Norman-w/smd-component-storage-book/output/3d-print/0603_tape_page_12mm_label12_x1c_petg_v1.3mf

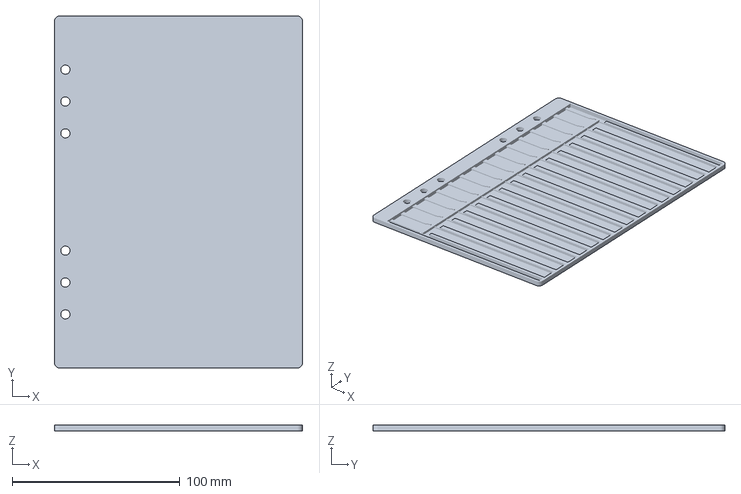
[picture p15: CAD file, 2026-09-22]
output/3d-print/0603_tape_page_12mm_label12_x1c_petg_v1.3mf
148.0 x 210.0 x 3.45 mm
