Norman-w/smd-component-storage-book/output/3d-print/0603_fit_coupon_single_7_16mm_label12_v1.stl

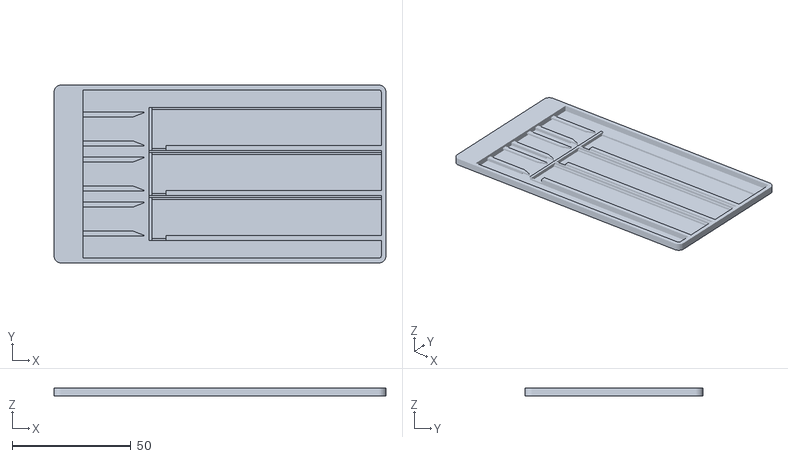
[picture p16: CAD file, 2026-09-22]
output/3d-print/0603_fit_coupon_single_7_16mm_label12_v1.stl
140.0 x 75.0 x 3.45
