Norman-w/smd-component-storage-book/output/3d-print/0603_tape_page_v9_convex_label_mouth.stl

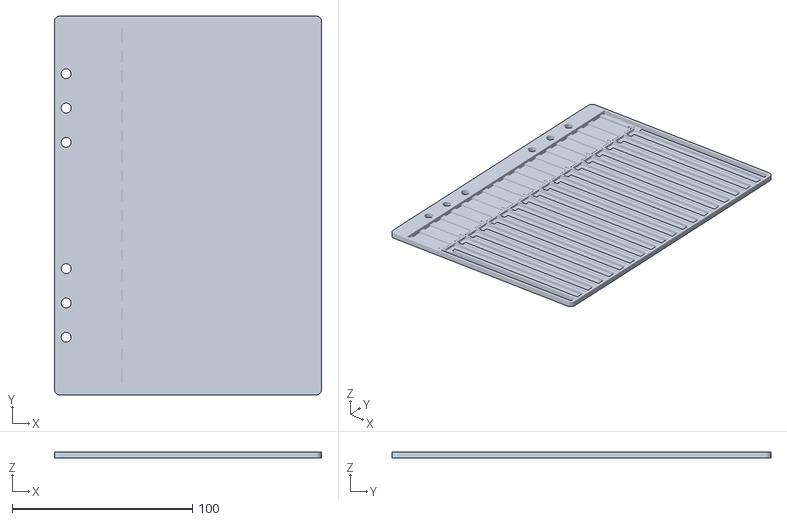
[picture p17: CAD file, 2026-09-20]
output/3d-print/0603_tape_page_v9_convex_label_mouth.stl
148.0 x 210.0 x 3.45
