Norman-w/smd-component-storage-book/output/3d-print/0603_tape_page_v5_thin_partition_x1c_safe.stl

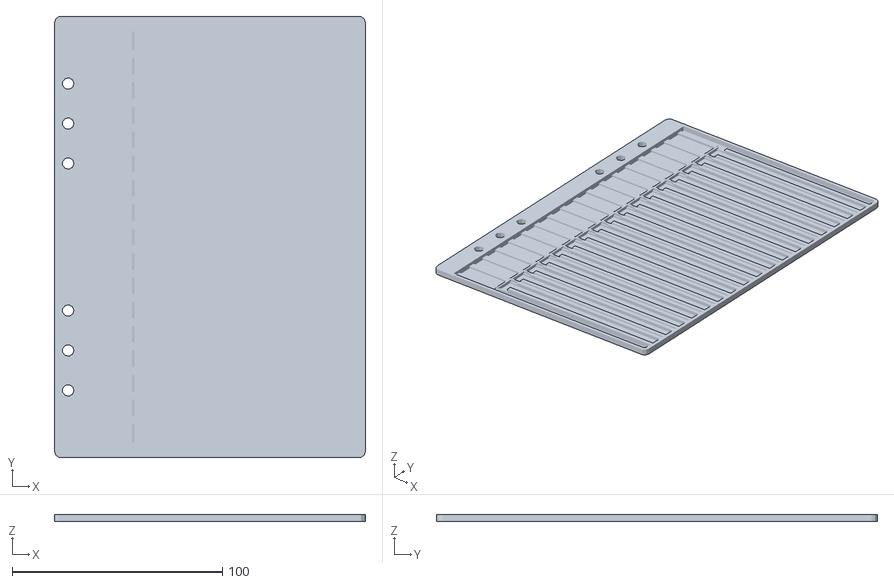
[picture p18: CAD file, 2026-09-20]
output/3d-print/0603_tape_page_v5_thin_partition_x1c_safe.stl
148.0 x 210.0 x 3.45
