Norman-w/smd-component-storage-book/output/3d-print/0603_tape_page_v3.stl

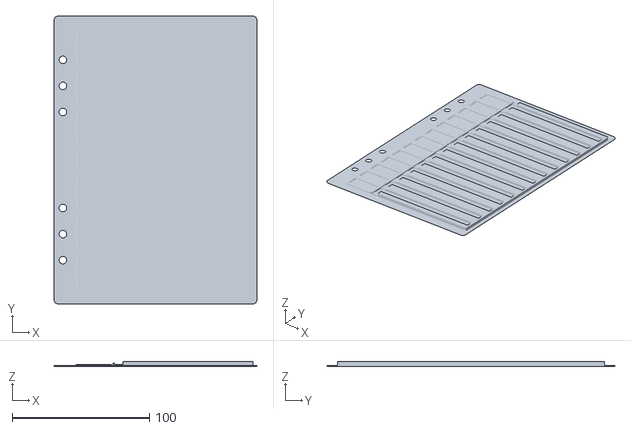
[picture p21: CAD file, 2026-09-20]
output/3d-print/0603_tape_page_v3.stl
148.0 x 210.0 x 3.45
