Norman-w/smd-component-storage-book/output/3d-print/0603_fit_coupon_single_7_v3.stl

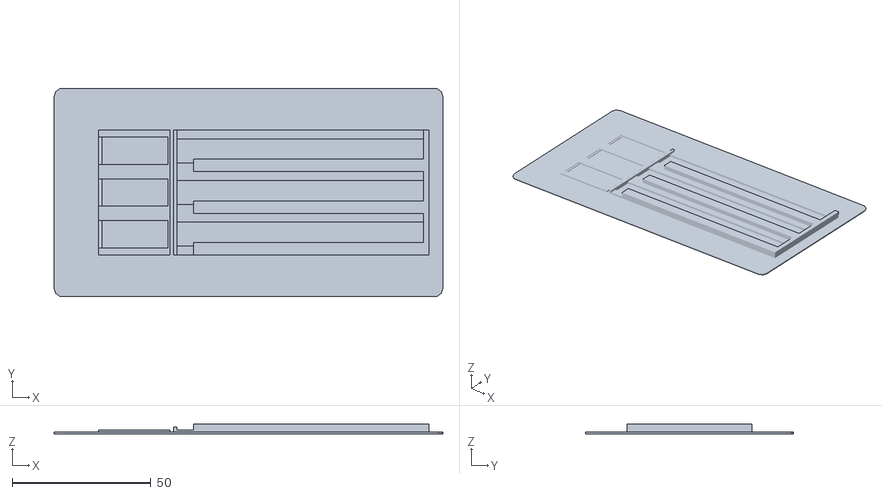
[picture p22: CAD file, 2026-09-20]
output/3d-print/0603_fit_coupon_single_7_v3.stl
140.0 x 74.7 x 3.45
