Norman-w/smd-component-storage-book/output/3d-print/0603_tape_page_v1_x1c_landscape.stl

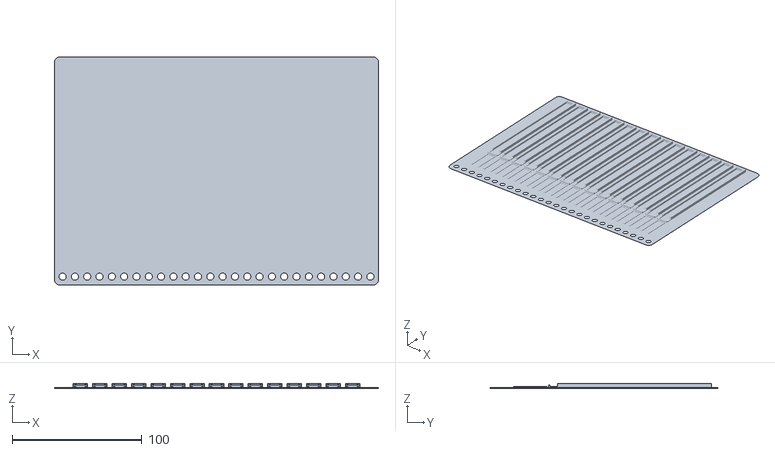
[picture p23: CAD file, 2026-09-20]
output/3d-print/0603_tape_page_v1_x1c_landscape.stl
250.0 x 176.0 x 3.55
