Norman-w/smd-component-storage-book/src/0603_tape_page_16mm_label12_tight_x1c_safe.scad

// X1C-safe wrapper for the compact 16 mm tape / 12 mm label page.
// The page geometry is shifted away from the X1C lower-left calibration area.

translate([54, 23, 0])
    import("../output/3d-print/0603_tape_page_16mm_label12_tight_v1.stl");
