Norman-w/smd-component-storage-book/output/verification/0603_16mm_label12_full_page_isometric.png

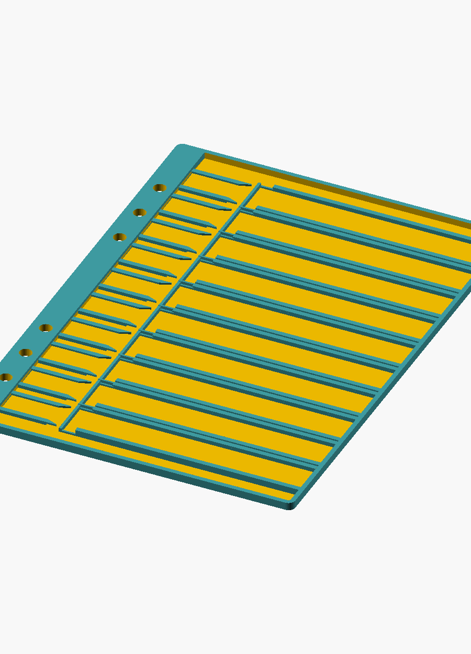
output/verification/0603_16mm_label12_full_page_isometric.png
