Norman-w/smd-component-storage-book/output/verification/0603_coupon_dual_iso.png

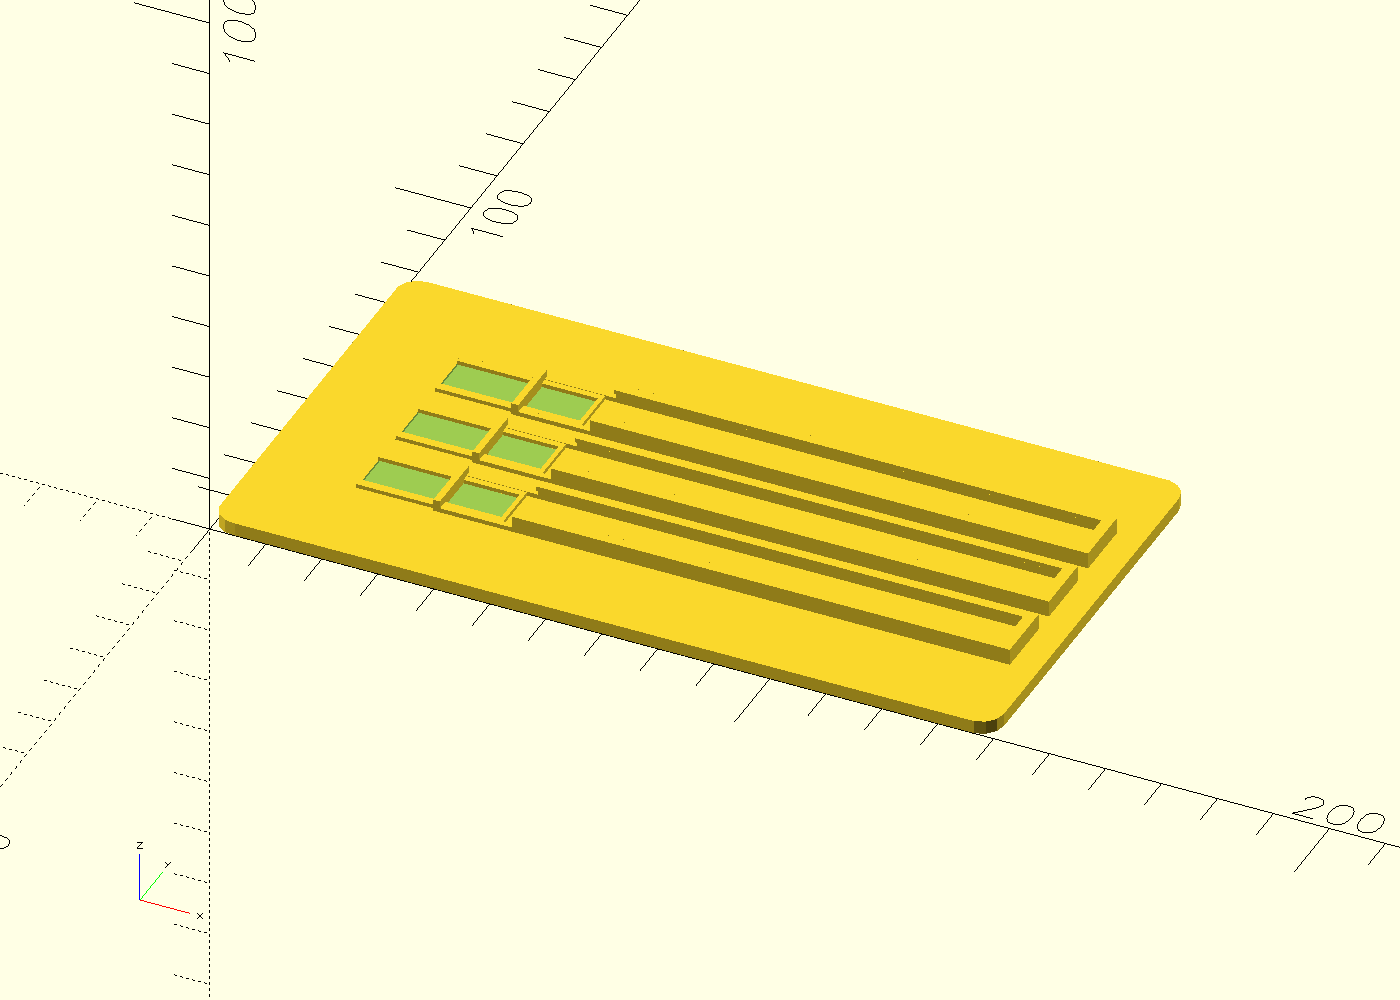
output/verification/0603_coupon_dual_iso.png
