Norman-w/smd-component-storage-book/output/verification/0603_coupon_dual_t_v2_top.png

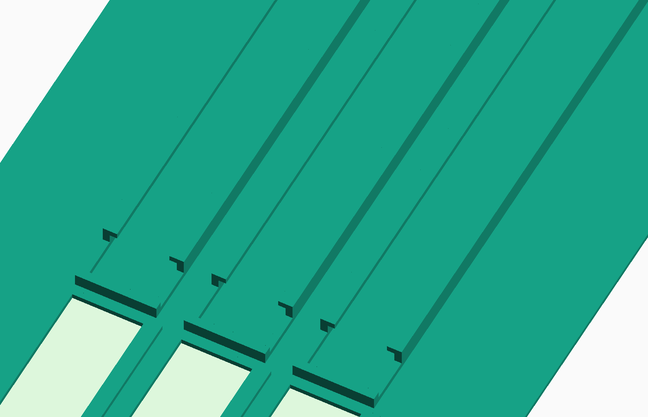
output/verification/0603_coupon_dual_t_v2_top.png
