Norman-w/smd-component-storage-book/output/verification/0603_fit_coupon_dual_t_v3_front.png

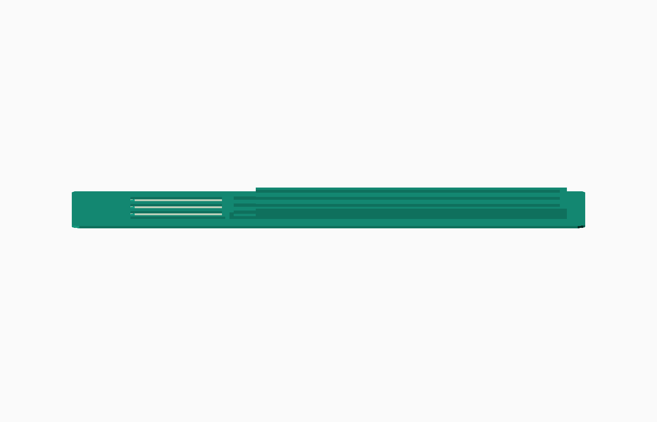
output/verification/0603_fit_coupon_dual_t_v3_front.png
