Norman-w/smd-component-storage-book/output/verification/0603_fit_coupon_dual_t_v4_right_label_iso.png

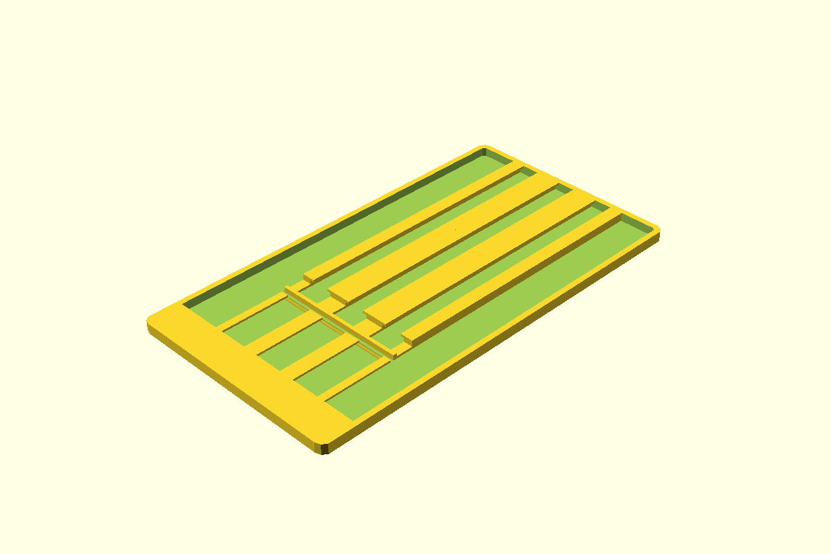
output/verification/0603_fit_coupon_dual_t_v4_right_label_iso.png
