Norman-w/smd-component-storage-book/output/verification/0603_fit_coupon_dual_t_v8_alternating_label_mouth_top.png

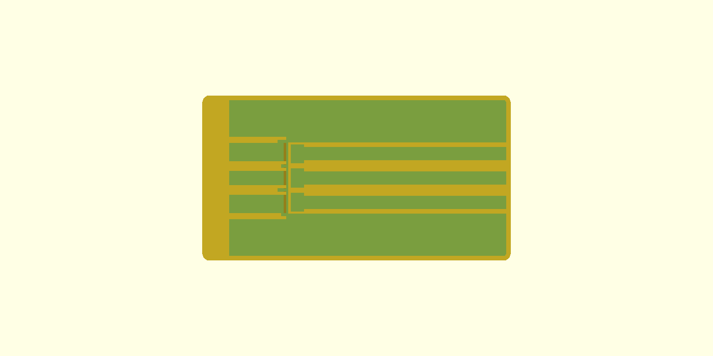
output/verification/0603_fit_coupon_dual_t_v8_alternating_label_mouth_top.png
