Norman-w/smd-component-storage-book/output/verification/0603_page_iso.png

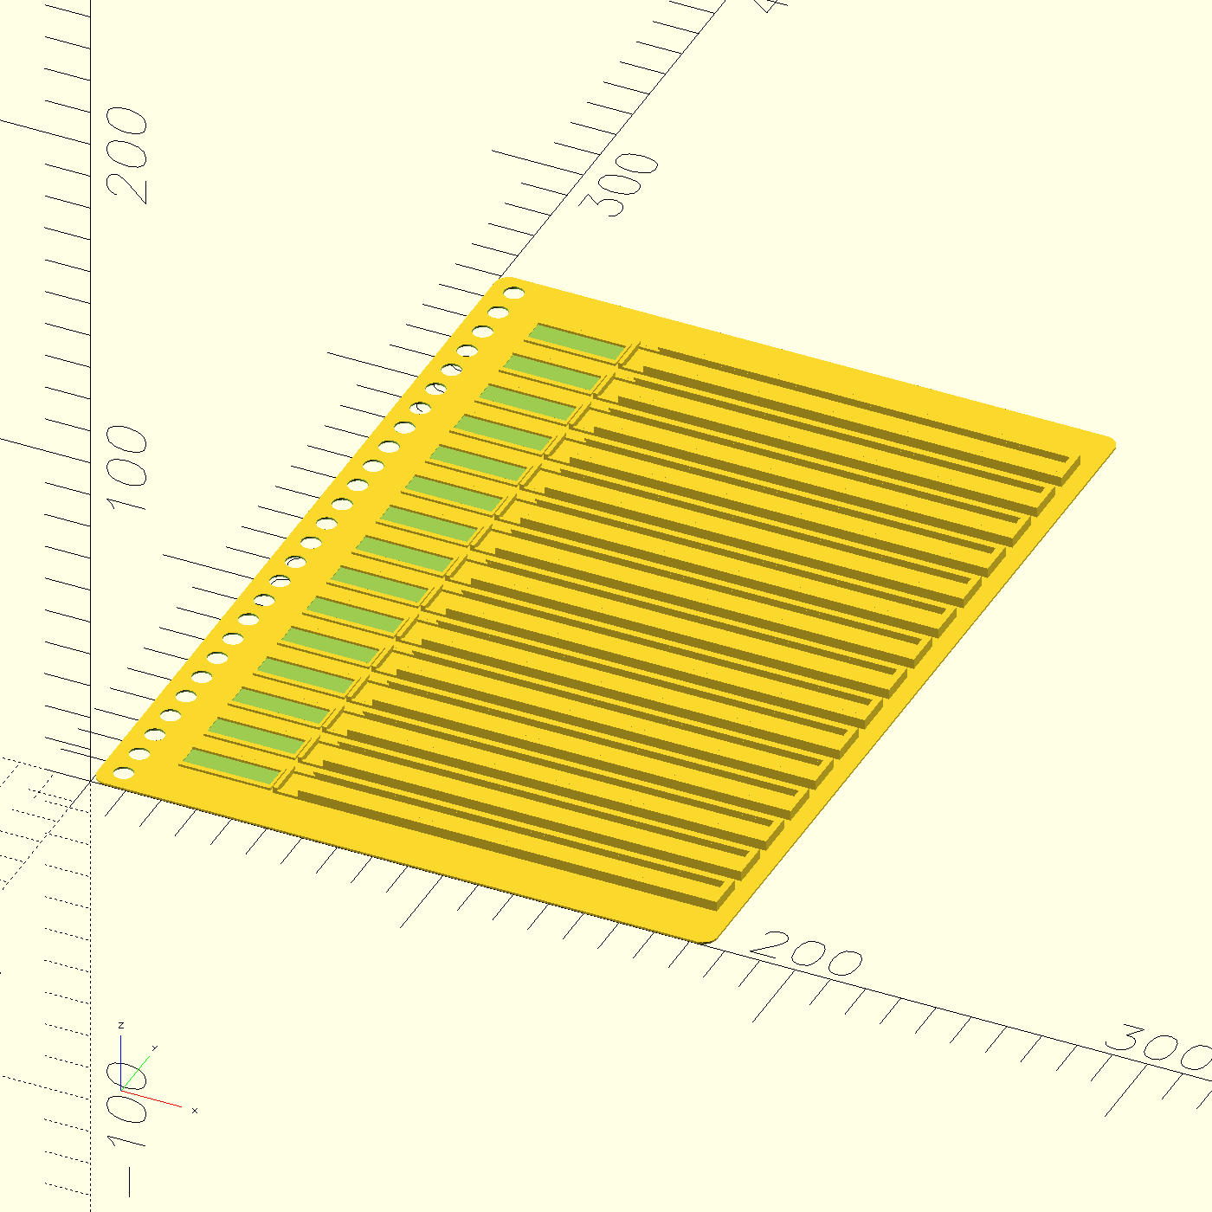
output/verification/0603_page_iso.png
