Norman-w/smd-component-storage-book/output/verification/0603_page_side.png

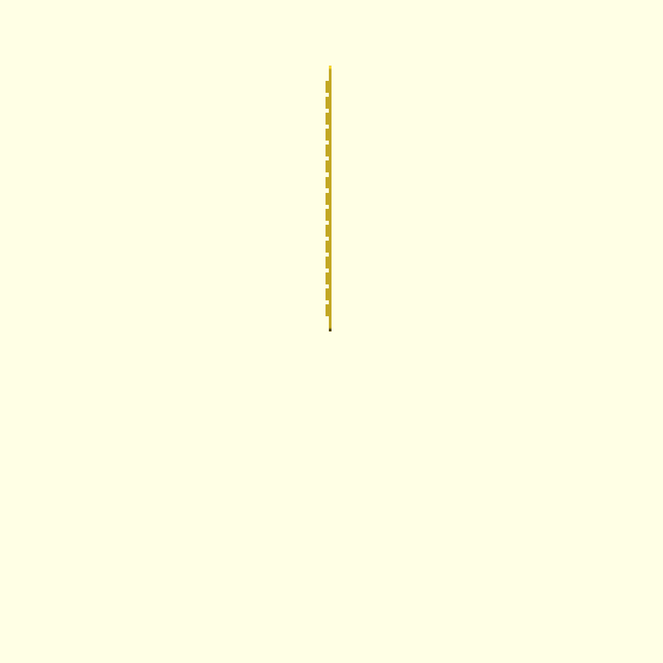
output/verification/0603_page_side.png
