Norman-w/smd-component-storage-book/output/verification/0603_tape_page_12mm_label12_full_page_top.png

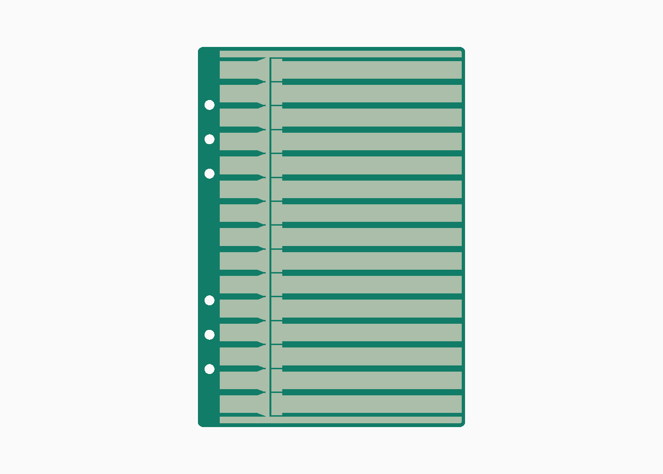
output/verification/0603_tape_page_12mm_label12_full_page_top.png
