Norman-w/smd-component-storage-book/output/verification/0603_tape_page_v3_perimeter_iso.png

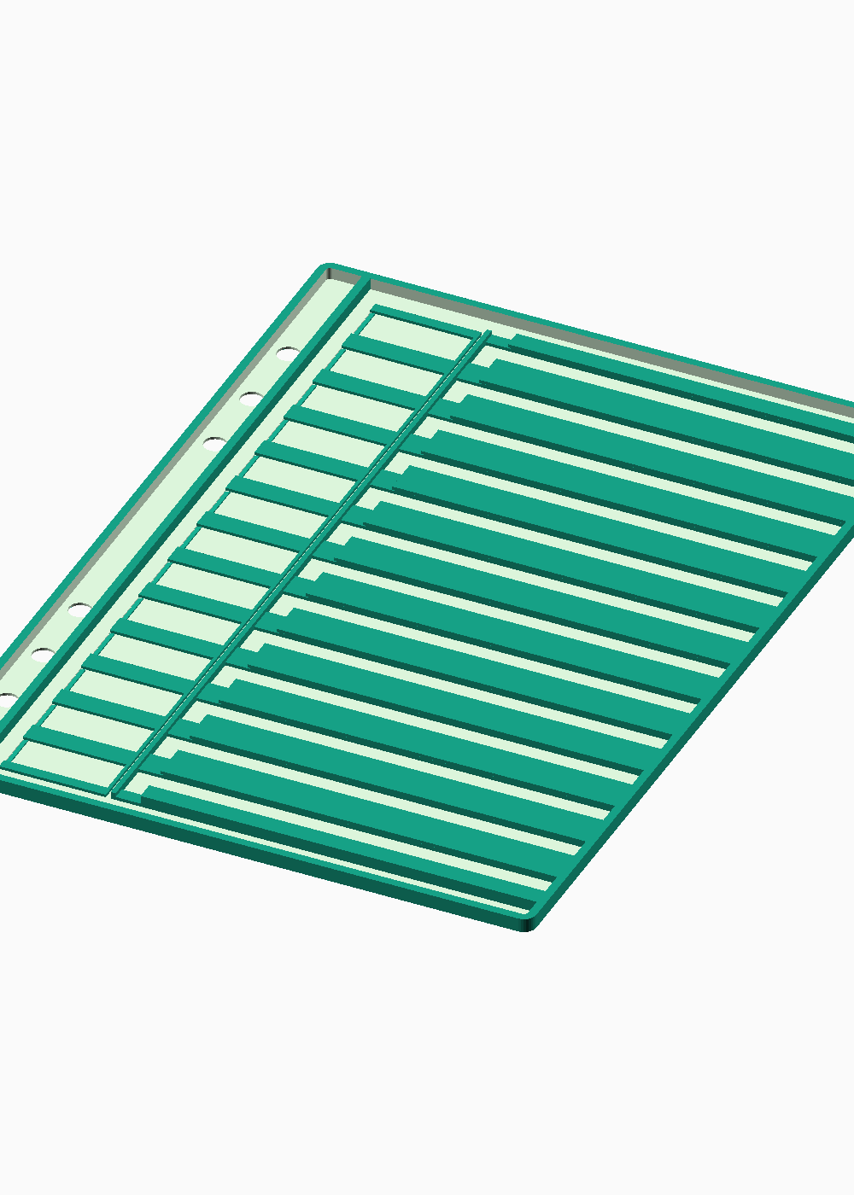
output/verification/0603_tape_page_v3_perimeter_iso.png
