Norman-w/smd-component-storage-book/output/verification/0603_tape_page_v4_right_label_iso.png

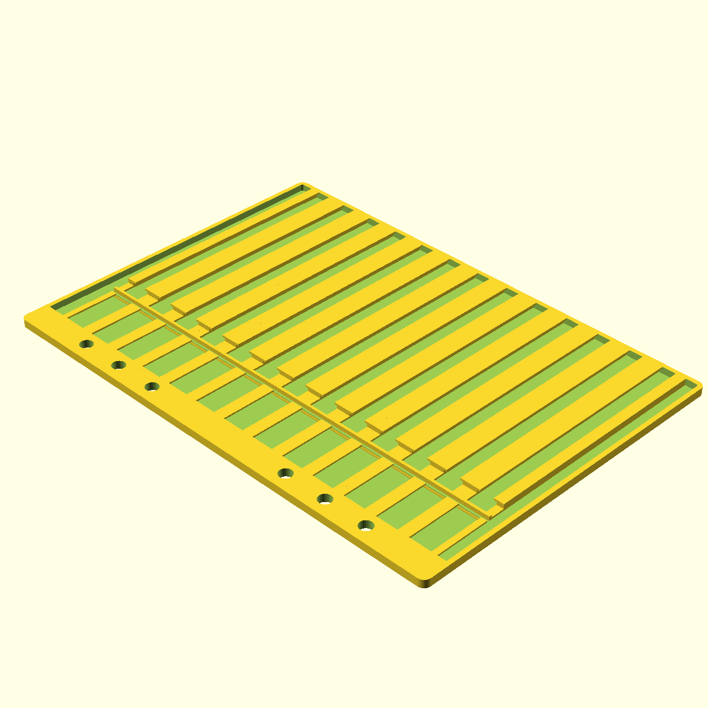
output/verification/0603_tape_page_v4_right_label_iso.png
