Norman-w/smd-component-storage-book/output/verification/0603_tape_page_v5_thin_partition_side.png

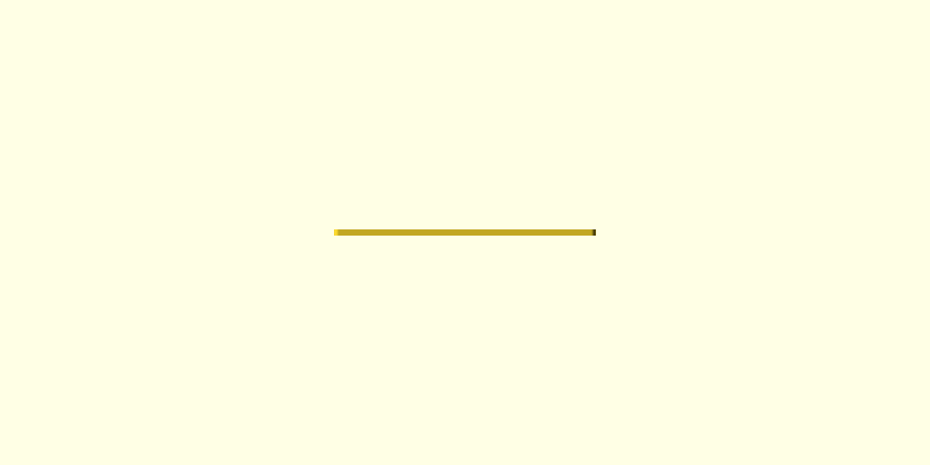
output/verification/0603_tape_page_v5_thin_partition_side.png
