Norman-w/smd-component-storage-book/output/verification/0603_tape_page_v7_label_entry_relief_front.png

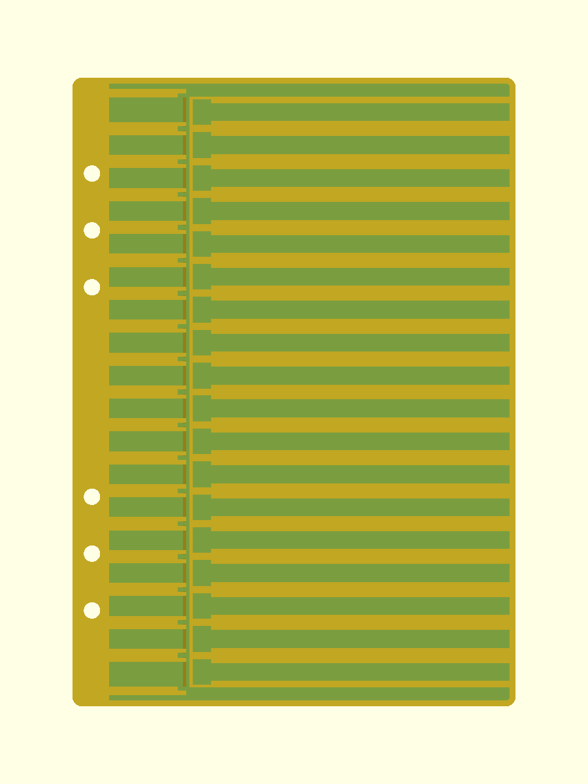
output/verification/0603_tape_page_v7_label_entry_relief_front.png
