Norman-w/smd-component-storage-book/output/verification/b5-variants/0603_tape_page_b5_12mm_top.png

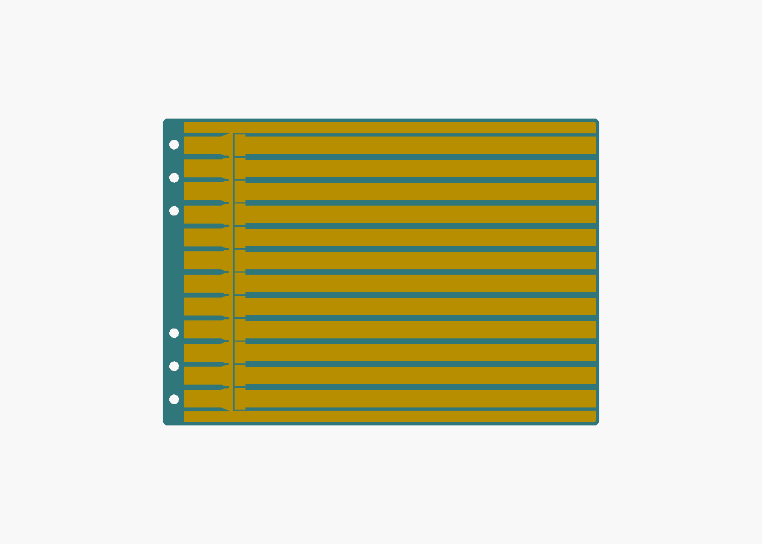
output/verification/b5-variants/0603_tape_page_b5_12mm_top.png
