Norman-w/smd-component-storage-book/output/verification/platform-release/0603_tape_page_8mm_label9_top.png

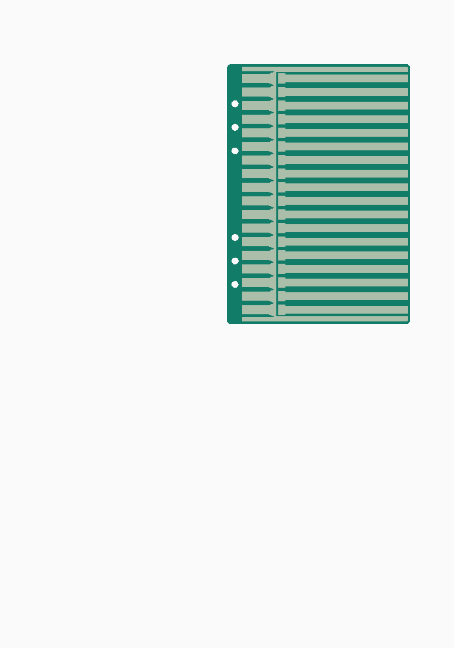
output/verification/platform-release/0603_tape_page_8mm_label9_top.png
