Norman-w/smd-component-storage-book/output/verification/platform-release/0603_tape_page_16mm_label12_tight_iso.png

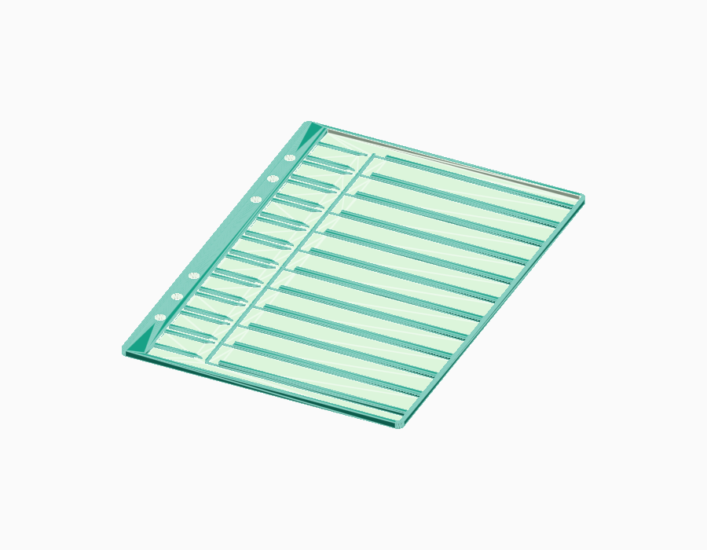
output/verification/platform-release/0603_tape_page_16mm_label12_tight_iso.png
