Norman-w/smd-component-storage-book/output/verification/top2.png

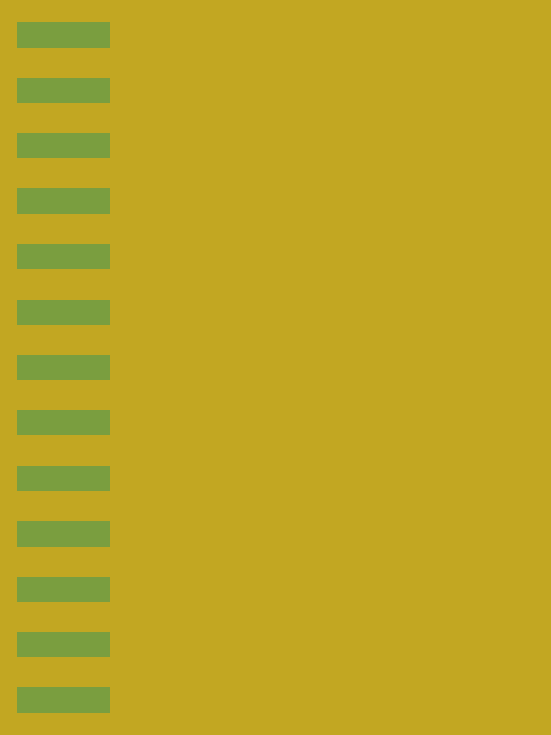
output/verification/top2.png
