Norman-w/smd-component-storage-book/output/verification/v22-render/full_page_isometric.png

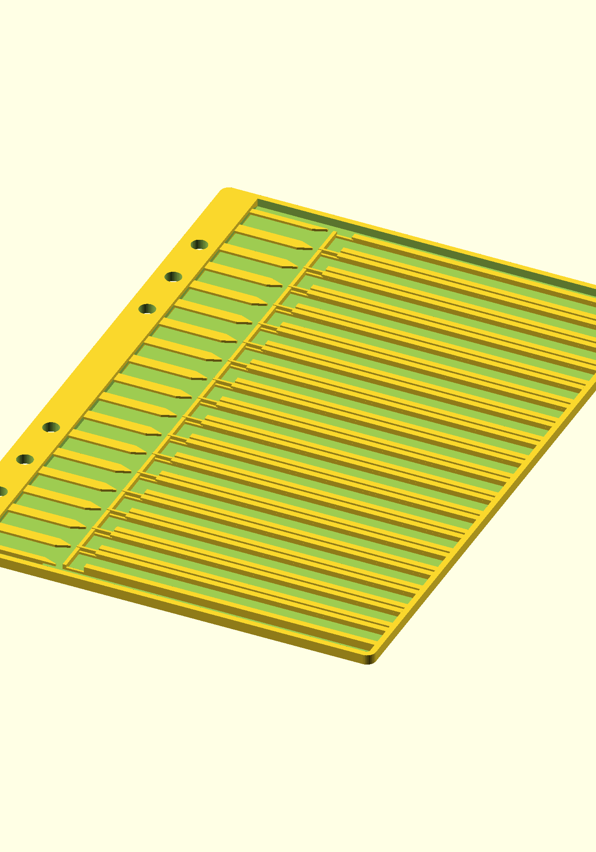
output/verification/v22-render/full_page_isometric.png
