Norman-w/smd-component-storage-book/output/verification/v22-render/full_page_top_v2.png

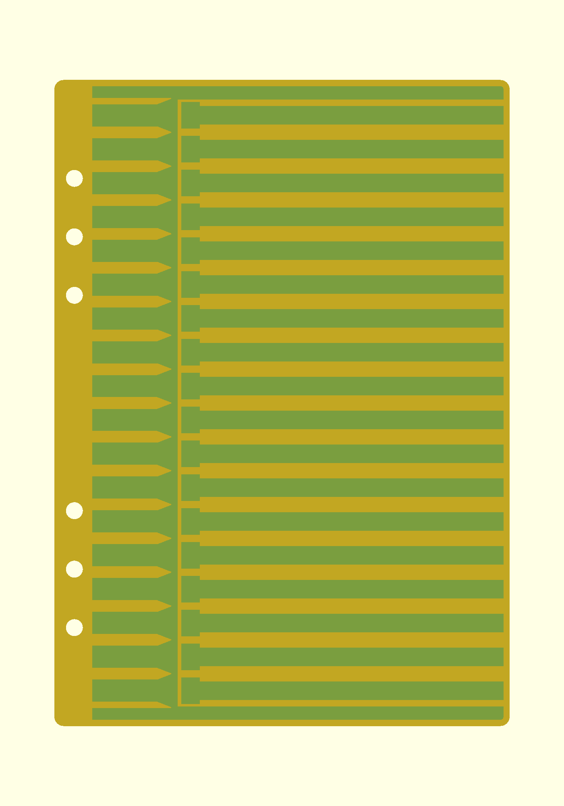
output/verification/v22-render/full_page_top_v2.png
