Norman-w/smd-component-storage-book/output/verification/v22-render/label_detail.png

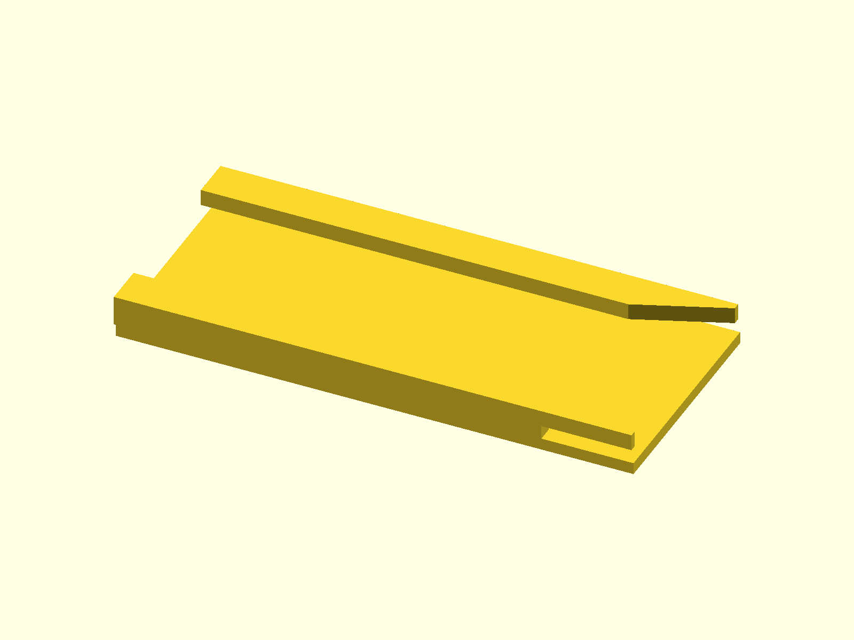
output/verification/v22-render/label_detail.png
