Norman-w/smd-component-storage-book/output/verification/wide-variants/0603_tape_page_24mm_iso.png

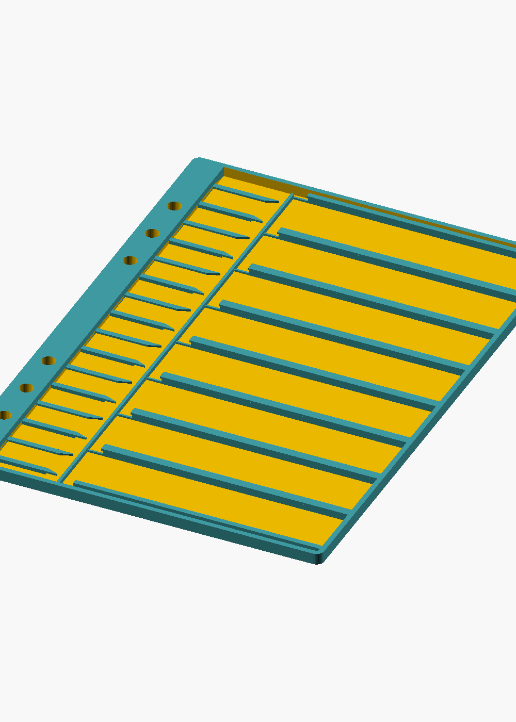
output/verification/wide-variants/0603_tape_page_24mm_iso.png
