Norman-w/smd-component-storage-book/output/verification/wide-variants/0603_tape_page_24mm_top.png

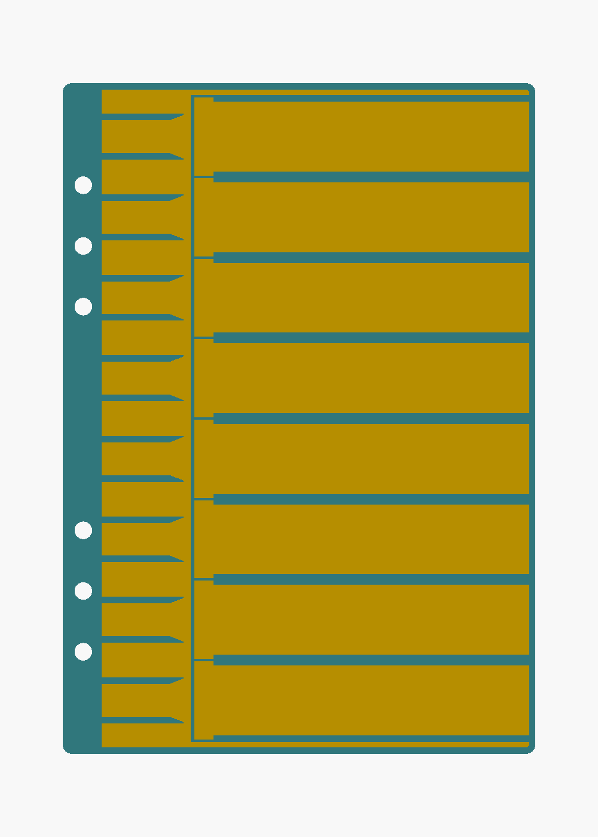
output/verification/wide-variants/0603_tape_page_24mm_top.png
